sawaiz/artDecoEarrings/docs/layout-dim.png

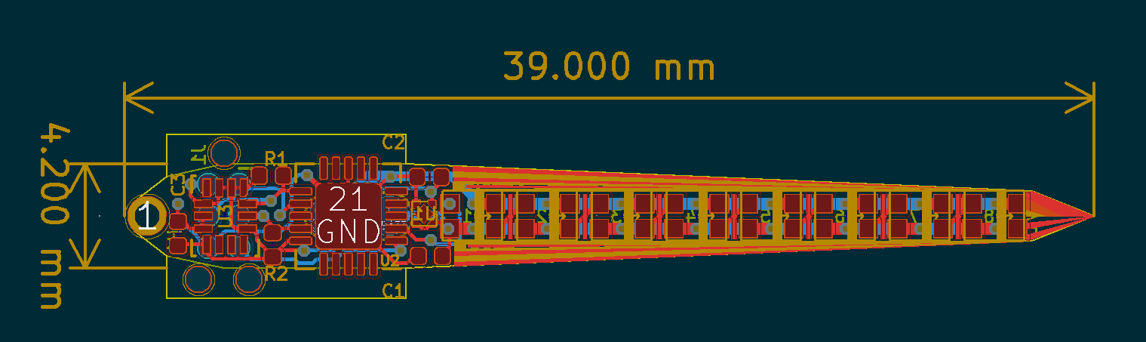
docs/layout-dim.png
