sawaiz/artDecoEarrings/docs/layout-trim.png

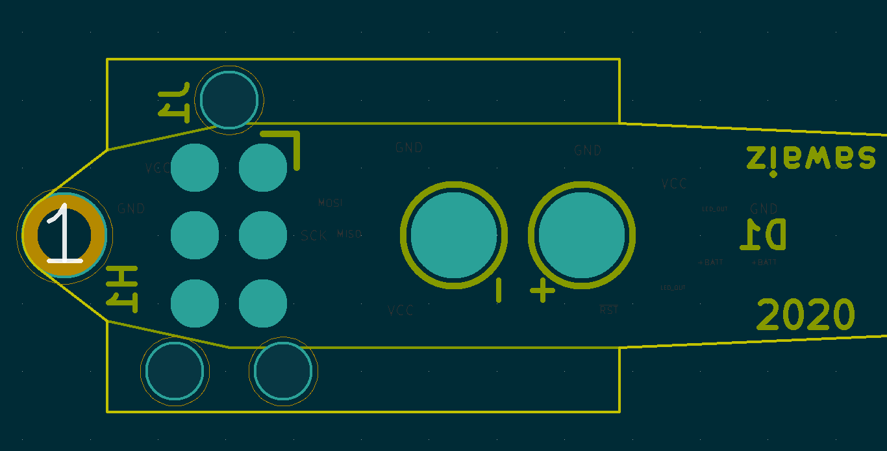
docs/layout-trim.png
