sawaiz/artDecoEarrings/docs/render-back.jpg

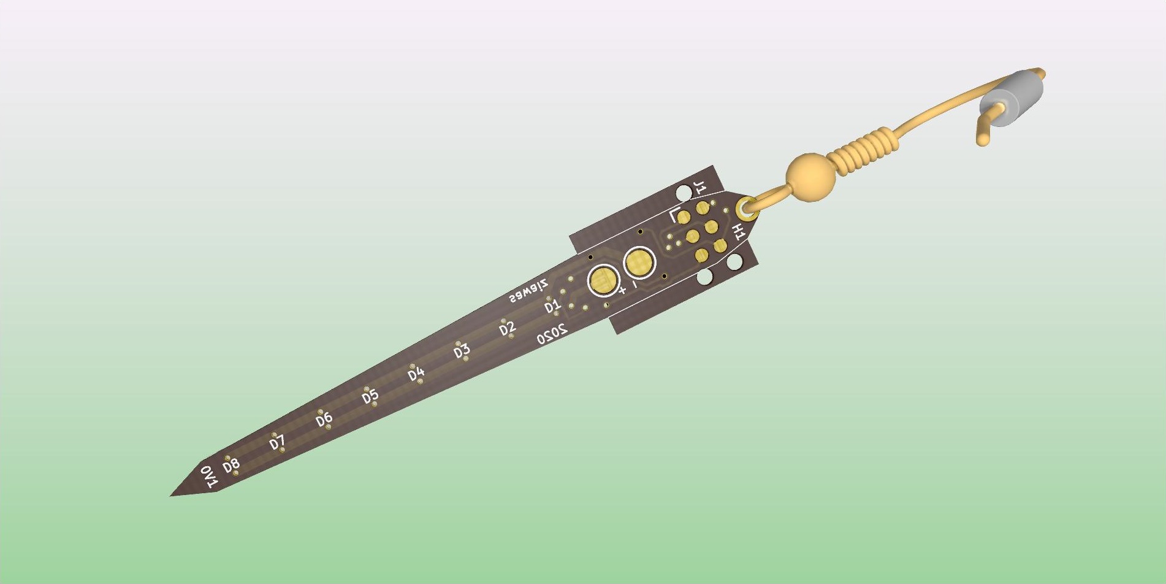
docs/render-back.jpg
