sawaiz/artDecoEarrings/docs/render-front.jpg

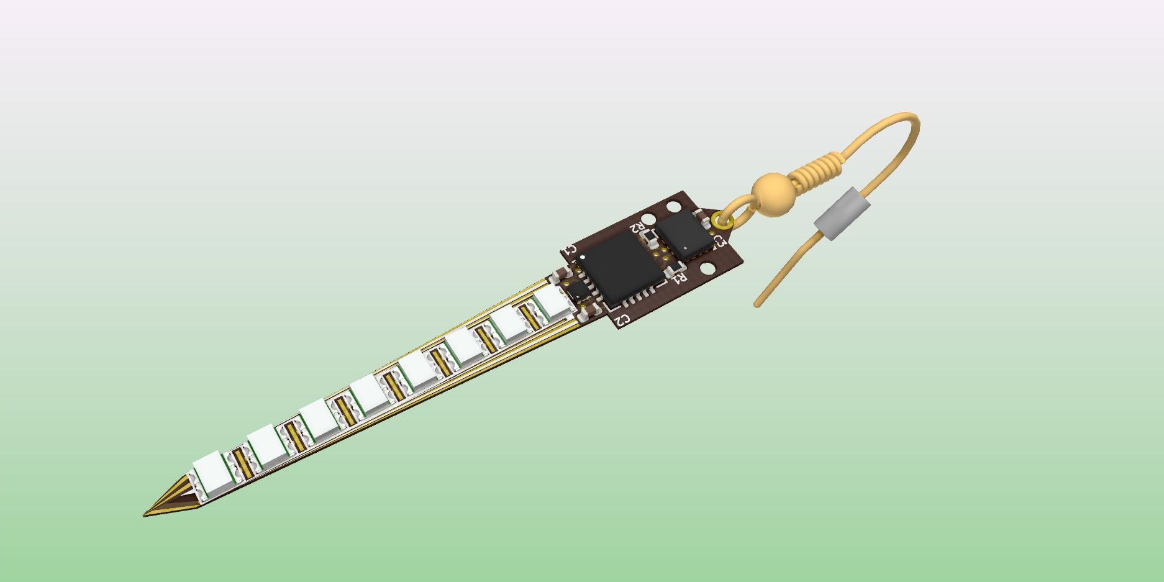
docs/render-front.jpg
