sawaiz/artDecoEarrings/docs/render-tip.png

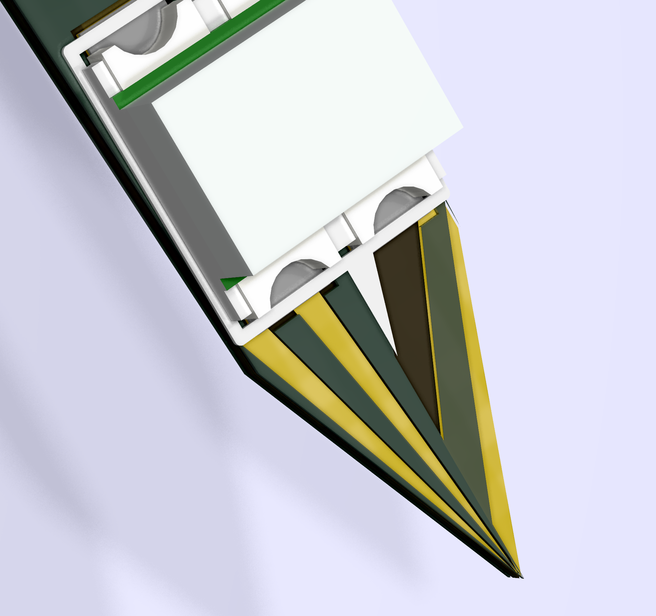
docs/render-tip.png
